citbrains/OpenPlatform/mechanism/OpenPlatform_ver3_0/dxf/GFRP/2mm/長穴減速_ホーン_1_2(1).dxf

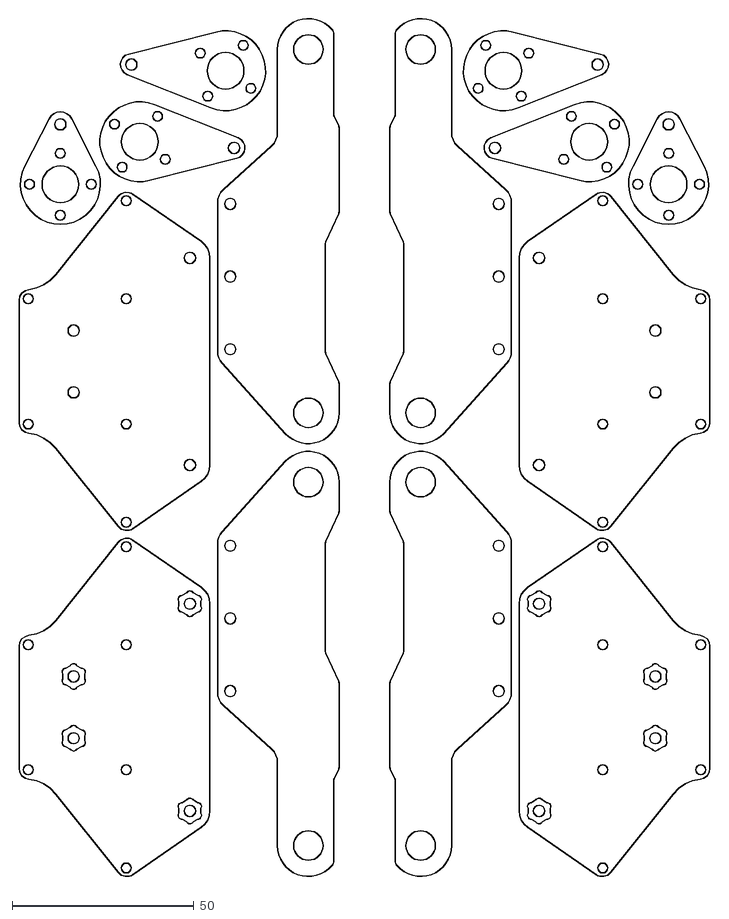
[picture p16: CAD file, 2018-04-28, an earlier design]
mechanism/OpenPlatform_ver3_0/dxf/GFRP/2mm/長穴減速_ホーン_1_2(1).dxf
191.7 x 237.5
