citbrains/OpenPlatform/vrep/OpenPlatform_ver1_0_Sim/dxf/POM/8mm/スペーサ.dxf

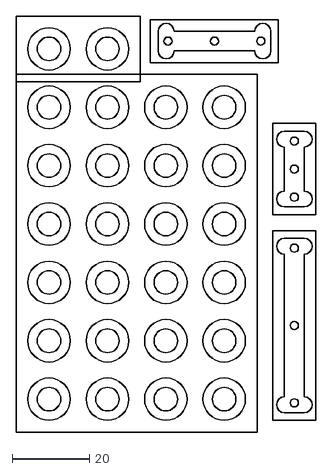
[picture p17: CAD file, 2017-08-26, an earlier design]
vrep/OpenPlatform_ver1_0_Sim/dxf/POM/8mm/スペーサ.dxf
77.5 x 107.6
